Cipulot/EC60/PCB/Rev_1_1_1/EC60-Rev_1_1_1.kicad_sch

## KiCad design PCB/Rev_1_1_1/EC60-Rev_1_1_1.kicad_sch (2024-06-05)

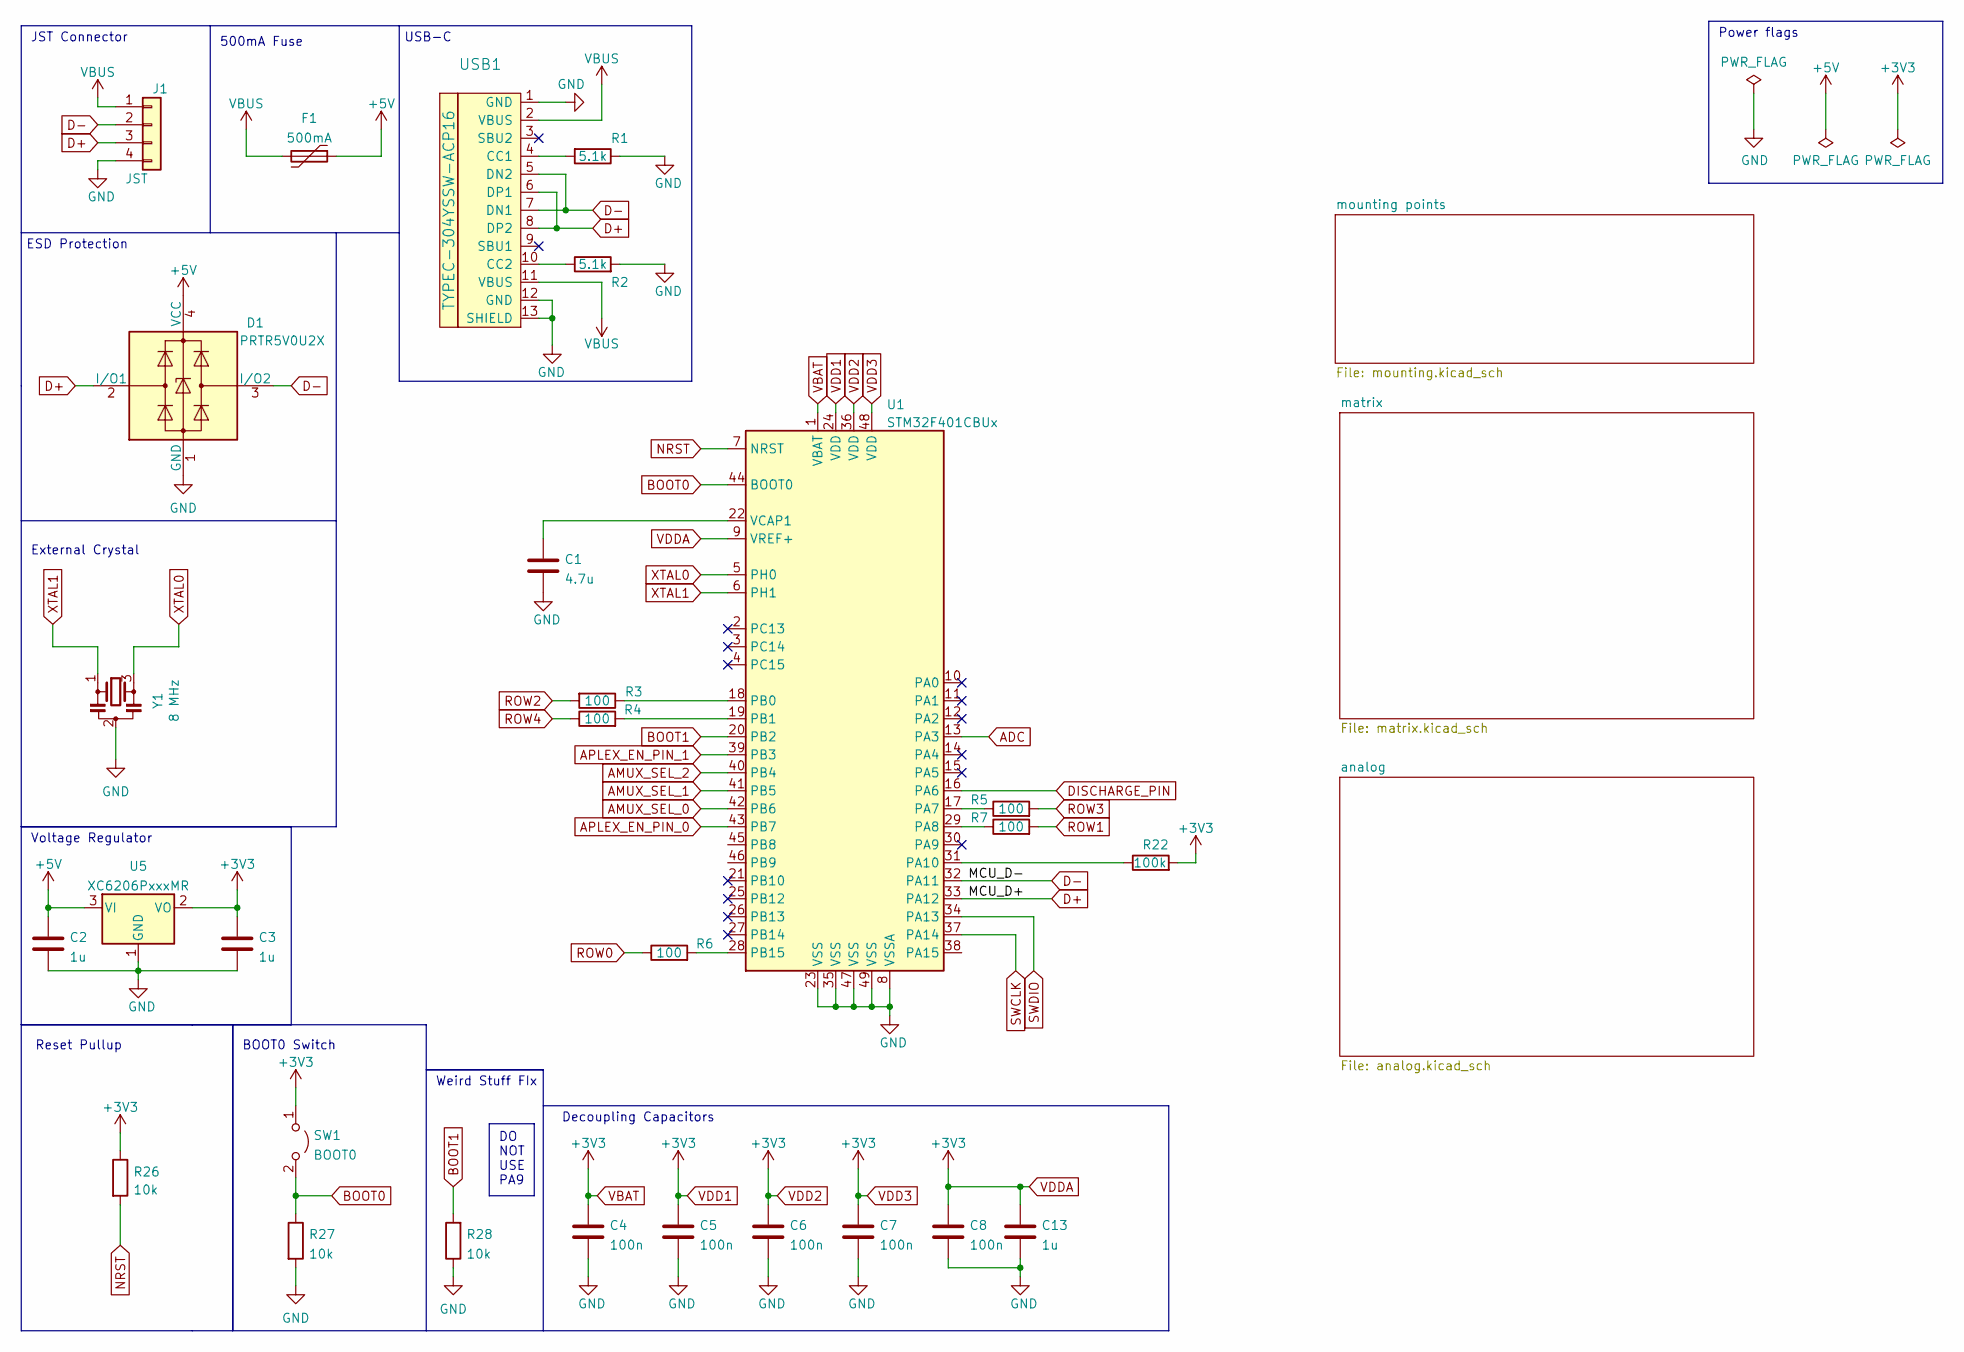
[picture p11: schematic EC60-Rev_1_1_1.kicad_sch]

Parts:
C1: 4.7u; C_0402_1005Metric; LCSC C23733
C2, C3, C13: 1u; C_0402_1005Metric; LCSC C52923
C4, C5, C6, C7, C8: 100n; C_0402_1005Metric; LCSC C307331
D1: PRTR5V0U2X; SOT-143; LCSC C2827688
F1: 500mA; Fuse_1206_3216Metric; LCSC C70076
J1: JST; JST-SR-4; LCSC C145956
R1, R2: 5.1k; R_0402_1005Metric; LCSC C25905
R3, R4, R5, R6, R7: 100; R_0402_1005Metric; LCSC C25076
R22: 100k; R_0402_1005Metric; LCSC C25741
R26, R27, R28: 10k; R_0402_1005Metric; LCSC C25744
SW1: BOOT0; PinHeader_1x02_P2.54mm_Vertical
U1: STM32F401CBUx; QFN-48-1EP_7x7mm_P0.5mm_EP5.6x5.6mm; LCSC C118825
U5: XC6206PxxxMR; SOT-23; LCSC C5446
USB1: TYPEC-304YSSW-ACP16; LCSC C2840392
Y1: 8 MHz; Resonator_SMD_Murata_CSTxExxV-3Pin_3.0x1.1mm; LCSC C907975

Connections:
+3V3: C3.1, C4.1, C5.1, C6.1, C7.1, C8.1, C13.1, R22.2, R26.1, SW1.1 (A), U1.1 (VBAT), U1.9 (VREF+), U1.24 (VDD), U1.36 (VDD), U1.48 (VDD), U5.2 (VO)
+5V: C2.1, D1.4 (VCC), F1.1, U5.3 (VI)
ADC: U1.13 (PA3)
AMUX_SEL_0: U1.42 (PB6)
AMUX_SEL_1: U1.41 (PB5)
AMUX_SEL_2: U1.40 (PB4)
APLEX_EN_PIN_0: U1.43 (PB7)
APLEX_EN_PIN_1: U1.39 (PB3)
BOOT0: R27.1, SW1.2 (B), U1.44 (BOOT0)
BOOT1: R28.2, U1.20 (PB2)
D+: D1.2 (I/O1), J1.3, U1.33 (PA12), USB1.6 (DP1), USB1.8 (DP2)
D-: D1.3 (I/O2), J1.2, U1.32 (PA11), USB1.5 (DN2), USB1.7 (DN1)
DISCHARGE_PIN: U1.16 (PA6)
GND: C1.2, C2.2, C3.2, C4.2, C5.2, C6.2, C7.2, C8.2, C13.2, D1.1 (GND), J1.4, R1.1, R2.2, R27.2, R28.1, U1.8 (VSSA), U1.23 (VSS), U1.35 (VSS), U1.47 (VSS), U1.49 (VSS), U5.1 (GND), USB1.1 (GND), USB1.12 (GND), USB1.13 (SHIELD), Y1.2
NRST: R26.2, U1.7 (NRST)
unnamed: C1.1, U1.22 (VCAP1)
unnamed: R1.2, USB1.4 (CC1)
unnamed: R2.1, USB1.10 (CC2)
unnamed: R3.1, U1.18 (PB0)
unnamed: R4.2, U1.19 (PB1)
unnamed: R5.1, U1.17 (PA7)
unnamed: R6.2, U1.28 (PB15)
unnamed: R7.1, U1.29 (PA8)
unnamed: R22.1, U1.31 (PA10)
ROW0: R6.1
ROW1: R7.2
ROW2: R3.2
ROW3: R5.2
ROW4: R4.1
SWCLK: U1.37 (PA14)
SWDIO: U1.34 (PA13)
VBUS: F1.2, J1.1, USB1.2 (VBUS), USB1.11 (VBUS)
XTAL0: U1.5 (PH0), Y1.3
XTAL1: U1.6 (PH1), Y1.1

Notes on the sheet:
DO NOT USE PA9
Voltage Regulator
JST Connector
BOOT0 Switch
External Crystal
Weird Stuff FIx
Decoupling Capacitors
Power flags
500mA Fuse
USB-C
ESD Protection
Reset Pullup
