Cipulot/EC60/PCB/Rev_1_1_1/analog.kicad_sch

## KiCad design PCB/Rev_1_1_1/analog.kicad_sch (2024-06-05)

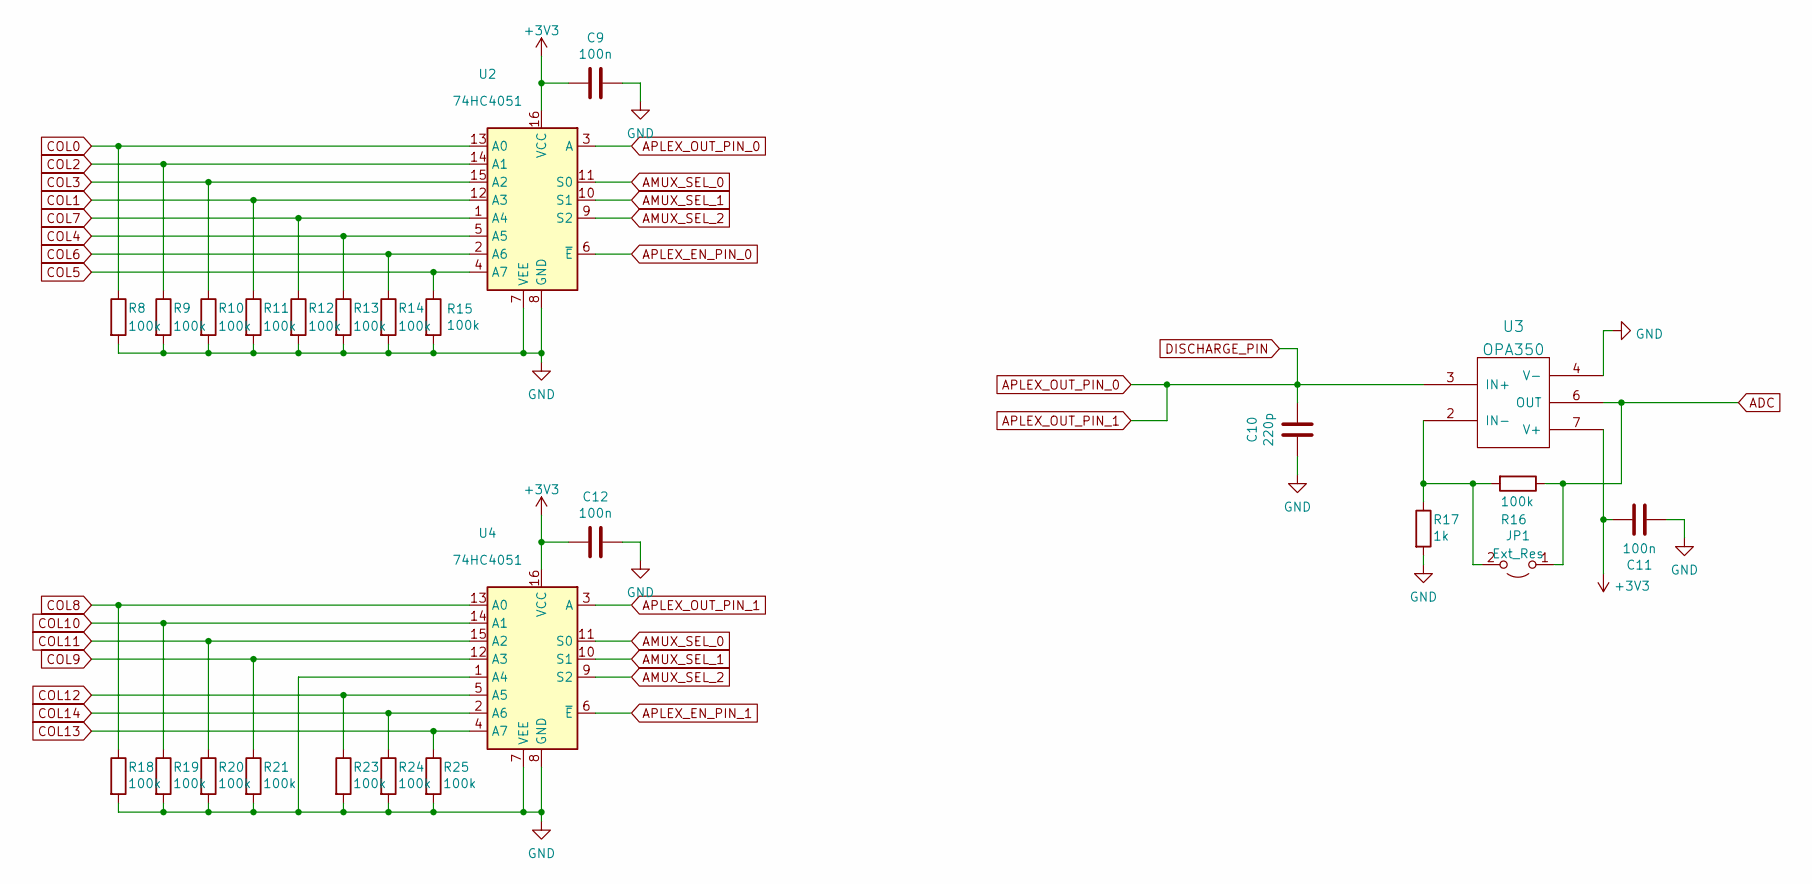
[picture p12: schematic analog.kicad_sch]

Parts:
C9, C11, C12: 100n; C_0402_1005Metric; LCSC C307331
C10: 220p; C_0402_1005Metric; LCSC C1530
JP1: Ext_Res; R_0603_1608Metric_Pad0.98x0.95mm_HandSolder
R8, R9, R10, R11, R12, R13, R14, R15, R16, R18, R19, R20, R21, R23, R24, R25: 100k; R_0402_1005Metric; LCSC C25741
R17: 1k; R_0402_1005Metric; LCSC C11702
U2, U4: 74HC4051; TSSOP16; LCSC C5645
U3: OPA350; SOIC-8_3.9x4.9mm_P1.27mm; LCSC C13388

Connections:
+3V3: C9.2, C11.2, C12.2, U2.16 (VCC), U3.7 (V+), U4.16 (VCC)
ADC: JP1.1 (A), R16.1, U3.6 (OUT)
AMUX_SEL_0: U2.11 (S0), U4.11 (S0)
AMUX_SEL_1: U2.10 (S1), U4.10 (S1)
AMUX_SEL_2: U2.9 (S2), U4.9 (S2)
APLEX_EN_PIN_0: U2.6 (~E)
APLEX_EN_PIN_1: U4.6 (~E)
APLEX_OUT_PIN_0: C10.1, U2.3 (A), U3.3 (IN+), U4.3 (A)
COL0: R8.1, U2.13 (A0)
COL1: R11.1, U2.12 (A3)
COL2: R9.1, U2.14 (A1)
COL3: R10.1, U2.15 (A2)
COL4: R13.1, U2.5 (A5)
COL5: R15.1, U2.4 (A7)
COL6: R14.1, U2.2 (A6)
COL7: R12.1, U2.1 (A4)
COL8: R18.1, U4.13 (A0)
COL9: R21.1, U4.12 (A3)
COL10: R19.1, U4.14 (A1)
COL11: R20.1, U4.15 (A2)
COL12: R23.1, U4.5 (A5)
COL13: R25.1, U4.4 (A7)
COL14: R24.1, U4.2 (A6)
GND: C9.1, C10.2, C11.1, C12.1, R8.2, R9.2, R10.2, R11.2, R12.2, R13.2, R14.2, R15.2, R17.2, R18.2, R19.2, R20.2, R21.2, R23.2, R24.2, R25.2, U2.7 (VEE), U2.8 (GND), U3.4 (V-), U4.1 (A4), U4.7 (VEE), U4.8 (GND)
unnamed: JP1.2 (B), R16.2, R17.1, U3.2 (IN-)
