Cipulot/EC60/PCB/Rev_1_1_1/matrix.kicad_sch

## KiCad design PCB/Rev_1_1_1/matrix.kicad_sch (2024-06-05)

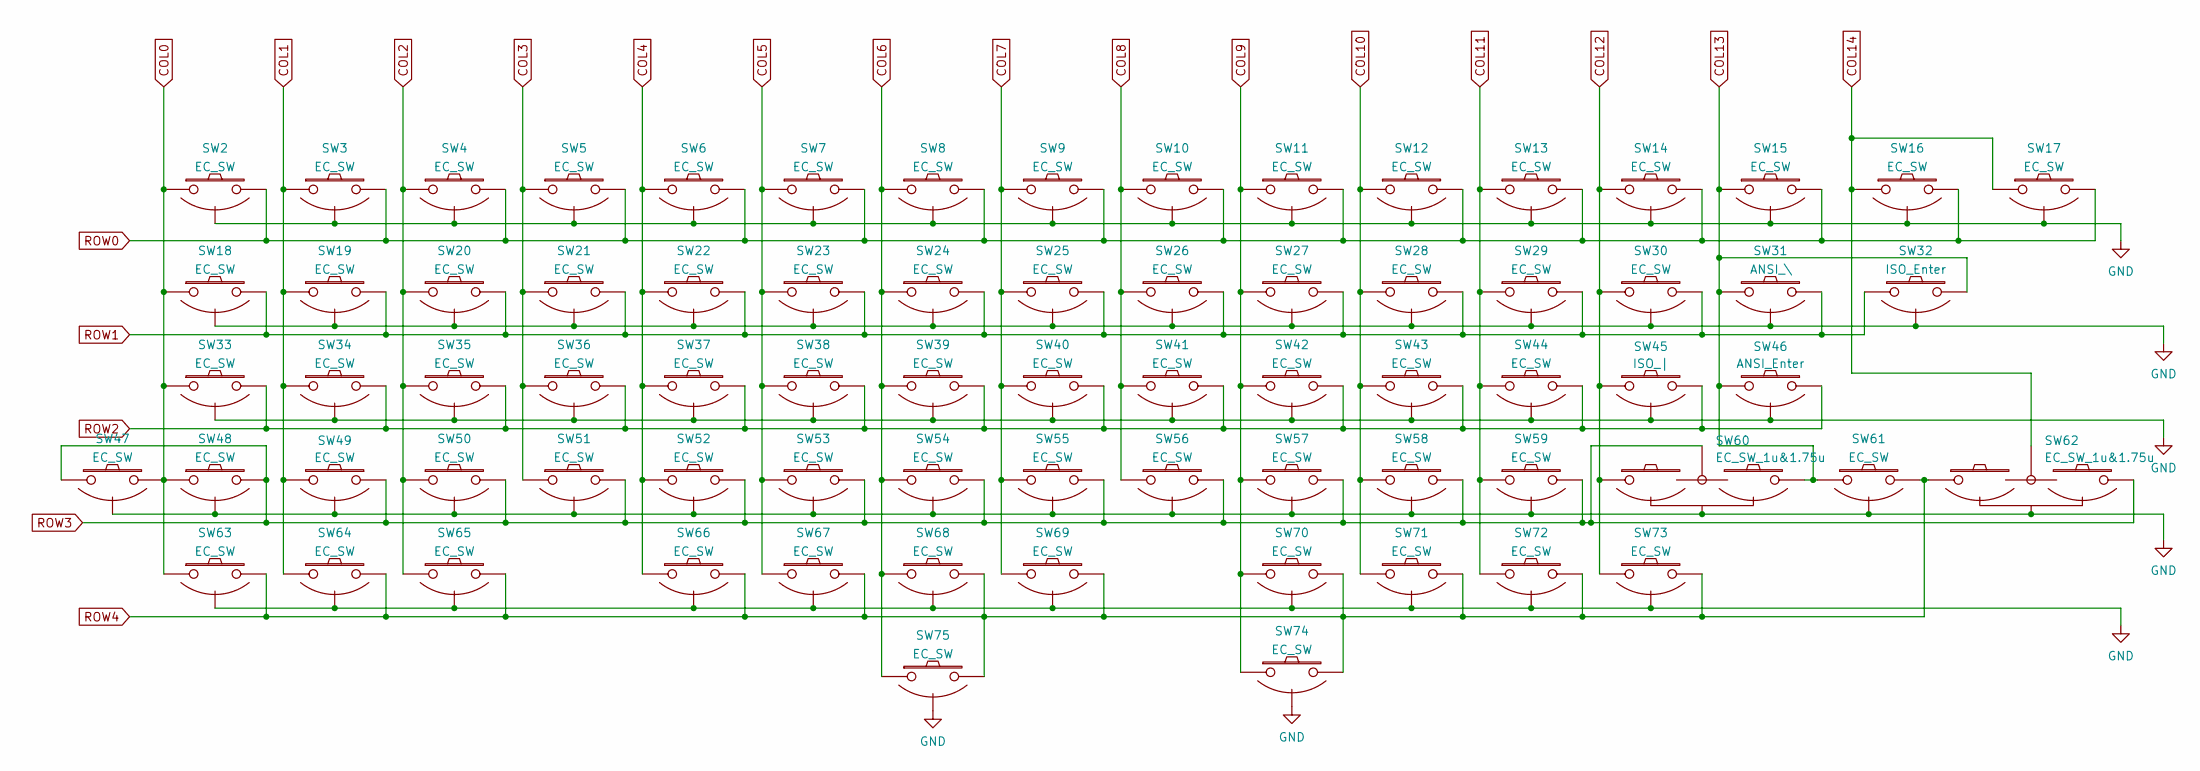
[picture p13: schematic matrix.kicad_sch]

Parts:
SW2, SW3, SW4, SW5, SW6, SW7, SW8, SW9, SW10, SW11, SW12, SW13, SW14, SW15, SW17, SW18, SW19, SW20, SW21, SW22, SW23, SW24, SW25, SW26, SW27, SW28, SW29, SW30, SW34, SW35, SW36, SW37, SW38, SW39, SW40, SW41, SW42, SW43, SW44, SW47, SW50, SW51, SW52, SW53, SW54, SW55, SW56, SW57, SW58, SW59, SW63, SW64, SW65, SW66, SW67, SW70, SW72, SW73, SW74, SW75: EC_SW; ecs_pad_1U_no_ring
SW16, SW61: EC_SW; ecs_pad_2U_no_ring
SW31: ANSI_\; ecs_pad_1U_no_ring
SW32: ISO_Enter; ecs_pad_2U_no_ring
SW33, SW68, SW69, SW71: EC_SW; ecs_pad_0.25U_spaced_no_ring
SW45: ISO_|; ecs_pad_1U_no_ring
SW46: ANSI_Enter; ecs_pad_2U_no_ring
SW48: EC_SW; ecs_pad_2U_no_ring_cut
SW49: EC_SW; ecs_pad_1U_no_ring_1u_edge_cut
SW60, SW62: EC_SW_1u&1.75u; ecs_pad_2.666U_spaced_no_ring_vertical

Connections:
COL0: SW2.1, SW18.1, SW33.1, SW47.2, SW48.1, SW63.1
COL1: SW3.1, SW19.1, SW34.1, SW49.2, SW64.1
COL2: SW4.1, SW20.1, SW35.1, SW50.1, SW65.1
COL3: SW5.1, SW21.1, SW36.1, SW51.1
COL4: SW6.1, SW22.1, SW37.1, SW52.1, SW66.1
COL5: SW7.1, SW23.1, SW38.1, SW53.1, SW67.1
COL6: SW8.1, SW24.1, SW39.1, SW54.1, SW68.1, SW75.1
COL7: SW9.1, SW25.1, SW40.1, SW55.1, SW69.1
COL8: SW10.1, SW26.1, SW41.1, SW56.1
COL9: SW11.1, SW27.1, SW42.1, SW57.1, SW70.1, SW74.1
COL10: SW12.1, SW28.1, SW43.1, SW58.1, SW71.1
COL11: SW13.1, SW29.1, SW44.1, SW59.1, SW72.1
COL12: SW14.1, SW30.1, SW45.1, SW60.1, SW73.1
COL13: SW15.1, SW31.1, SW32.2, SW46.2, SW60.3, SW61.1
COL14: SW16.1, SW17.1, SW62.2
GND: SW2.3 (SG), SW3.3 (SG), SW4.3 (SG), SW5.3 (SG), SW6.3 (SG), SW7.3 (SG), SW8.3 (SG), SW9.3 (SG), SW10.3 (SG), SW11.3 (SG), SW12.3 (SG), SW13.3 (SG), SW14.3 (SG), SW15.3 (SG), SW16.3 (SG), SW17.3 (SG), SW18.3 (SG), SW19.3 (SG), SW20.3 (SG), SW21.3 (SG), SW22.3 (SG), SW23.3 (SG), SW24.3 (SG), SW25.3 (SG), SW26.3 (SG), SW27.3 (SG), SW28.3 (SG), SW29.3 (SG), SW30.3 (SG), SW31.3 (SG), SW32.3 (SG), SW33.3 (SG), SW34.3 (SG), SW35.3 (SG), SW36.3 (SG), SW37.3 (SG), SW38.3 (SG), SW39.3 (SG), SW40.3 (SG), SW41.3 (SG), SW42.3 (SG), SW43.3 (SG), SW44.3 (SG), SW45.3 (SG), SW46.3 (SG), SW47.3 (SG), SW48.3 (SG), SW49.3 (SG), SW50.3 (SG), SW51.3 (SG), SW52.3 (SG), SW53.3 (SG), SW54.3 (SG), SW55.3 (SG), SW56.3 (SG), SW57.3 (SG), SW58.3 (SG), SW59.3 (SG), SW60.4 (SG), SW61.3 (SG), SW62.4 (SG), SW63.3 (SG), SW64.3 (SG), SW65.3 (SG), SW66.3 (SG), SW67.3 (SG), SW68.3 (SG), SW69.3 (SG), SW70.3 (SG), SW71.3 (SG), SW72.3 (SG), SW73.3 (SG), SW74.3 (SG), SW75.3 (SG)
ROW0: SW2.2, SW3.2, SW4.2, SW5.2, SW6.2, SW7.2, SW8.2, SW9.2, SW10.2, SW11.2, SW12.2, SW13.2, SW14.2, SW15.2, SW16.2, SW17.2
ROW1: SW18.2, SW19.2, SW20.2, SW21.2, SW22.2, SW23.2, SW24.2, SW25.2, SW26.2, SW27.2, SW28.2, SW29.2, SW30.2, SW31.2, SW32.1
ROW2: SW33.2, SW34.2, SW35.2, SW36.2, SW37.2, SW38.2, SW39.2, SW40.2, SW41.2, SW42.2, SW43.2, SW44.2, SW45.2, SW46.1
ROW3: SW47.1, SW48.2, SW49.1, SW50.2, SW51.2, SW52.2, SW53.2, SW54.2, SW55.2, SW56.2, SW57.2, SW58.2, SW59.2, SW60.2, SW62.3
ROW4: SW61.2, SW62.1, SW63.2, SW64.2, SW65.2, SW66.2, SW67.2, SW68.2, SW69.2, SW70.2, SW71.2, SW72.2, SW73.2, SW74.2, SW75.2
